ZSWatch/Extension-HW/production/extension-CHECKED/HTML/images/cat_pdf_drill_map_ZSWatch-Extension-NPTH_drill_map.png

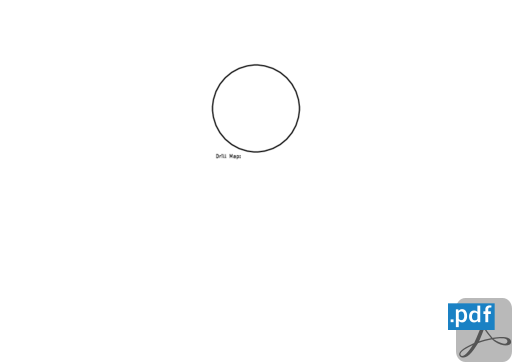
production/extension-CHECKED/HTML/images/cat_pdf_drill_map_ZSWatch-Extension-NPTH_drill_map.png
