ZSWatch/Extension-HW/production/extension-CHECKED/HTML/images/cat_png_3d_viewer_angled_top_ZSWatch-Extension-angled_top.png

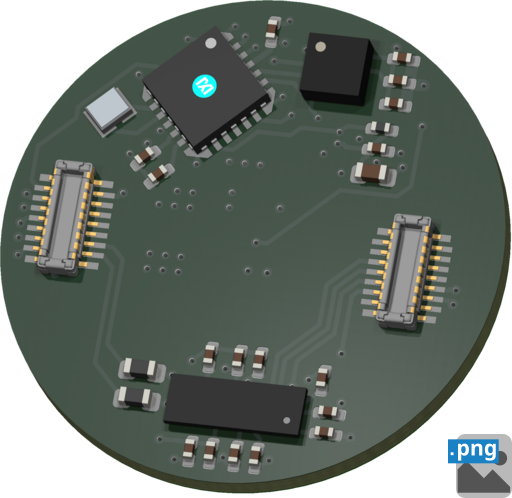
production/extension-CHECKED/HTML/images/cat_png_3d_viewer_angled_top_ZSWatch-Extension-angled_top.png
