ZSWatch/Extension-HW/production/extension-CHECKED/Manufacturing/Fabrication/ZSWatch-Extension-fabrication.pdf

# Top Fabrication (Scale 1:1)

# Heartrate-HW Fabrication Document

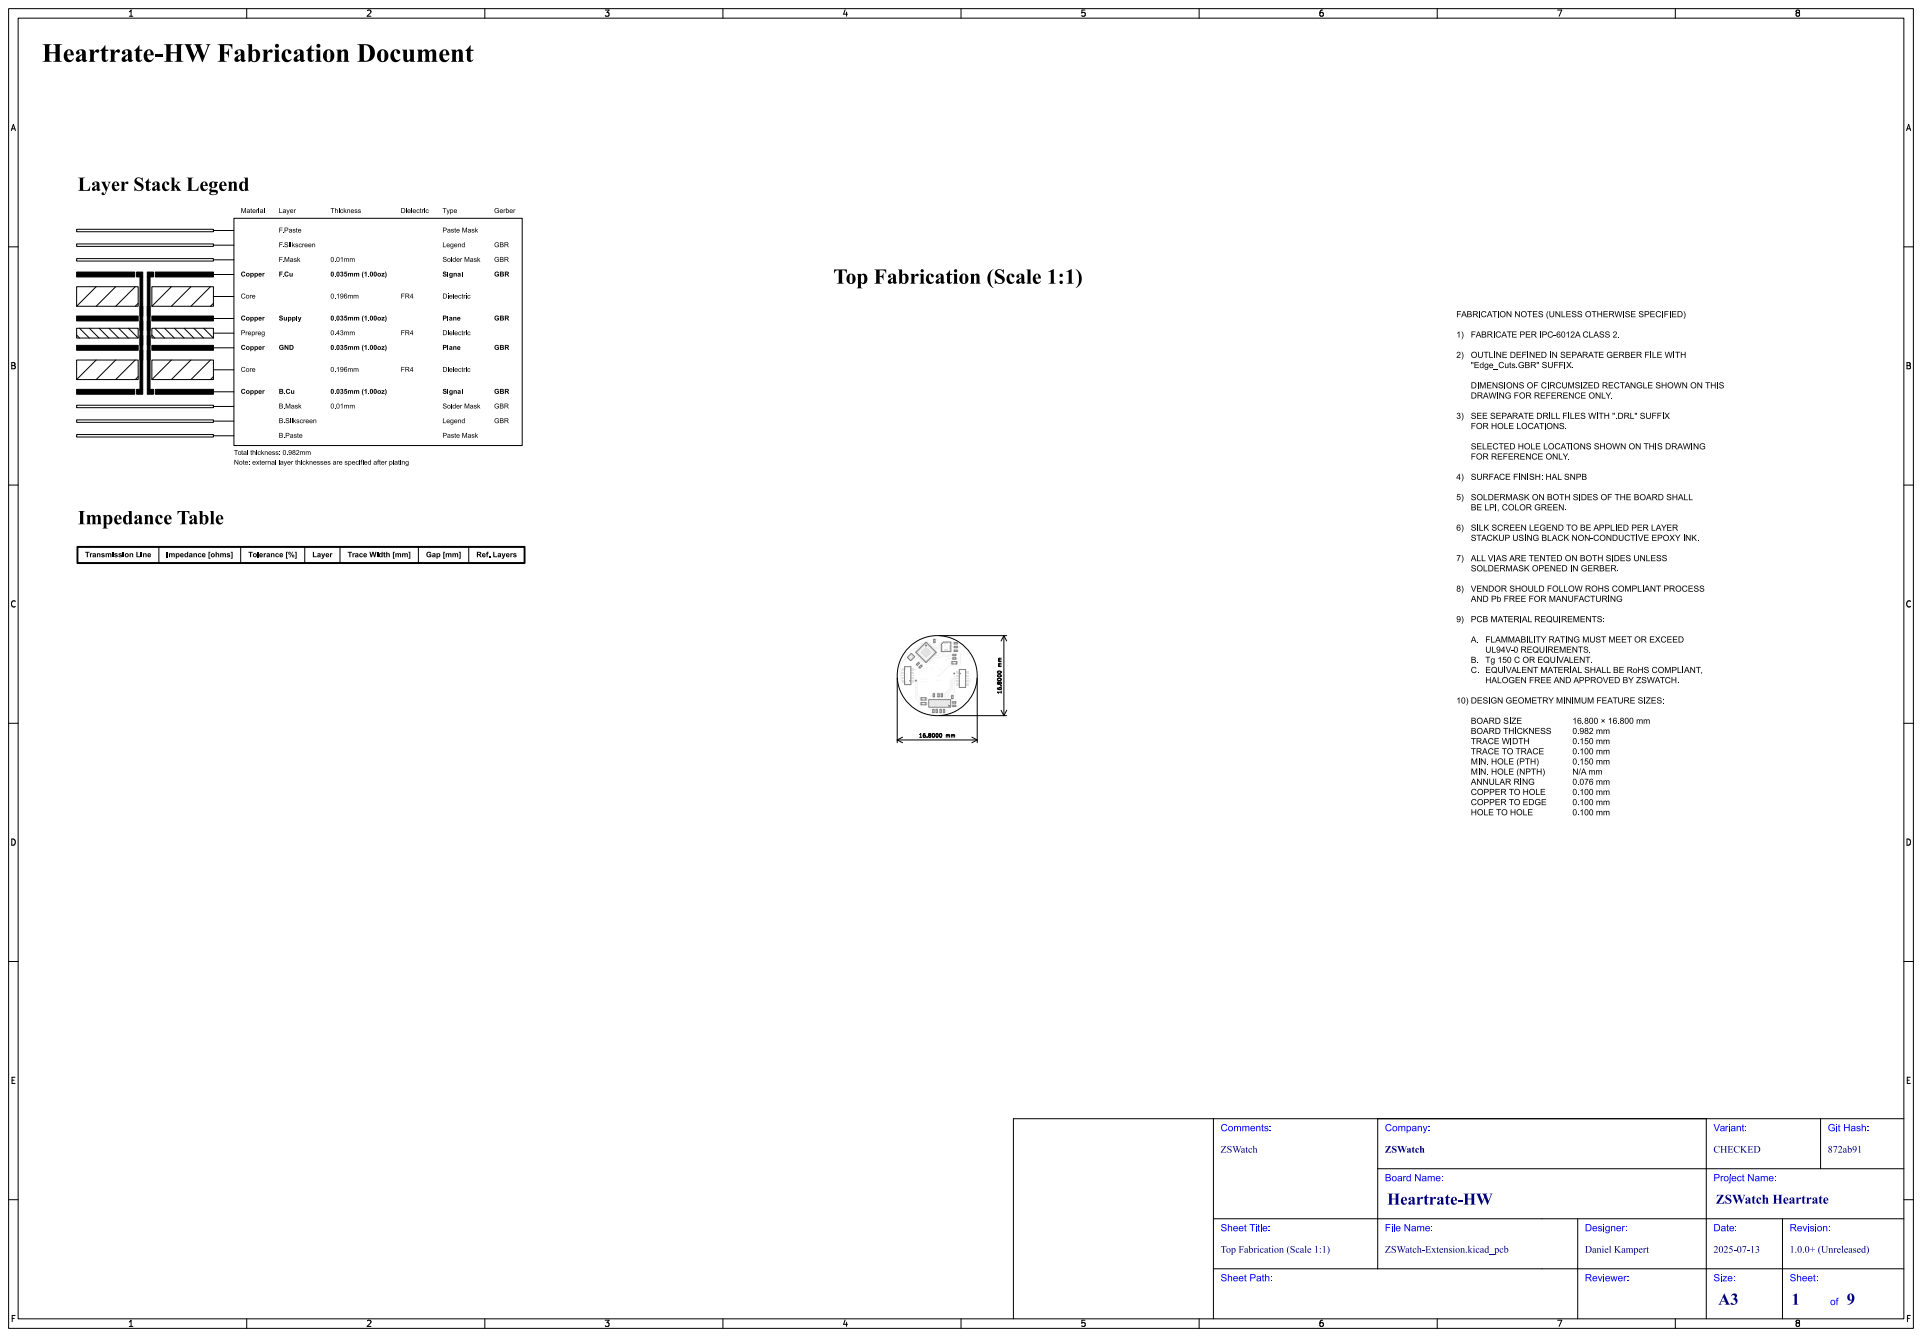
[picture p11: page 1]
Git Hash:; ZSWatch; Comments:; Sheet Path:; Sheet Title:; File Name:; Heartrate-HW; ZSWatch Heartrate; Company:; CHECKED; Variant:; Board Name:; ZSWatch-Extension.kicad_pcb; Daniel Kampert; Designer:; Reviewer:; Project Name:; Date:; 1.0.0+ (Unreleased); Revision:; Size:; Sheet:

Top Fabrication (Scale 1:1)

# Bottom Fabrication (Scale 1:1)

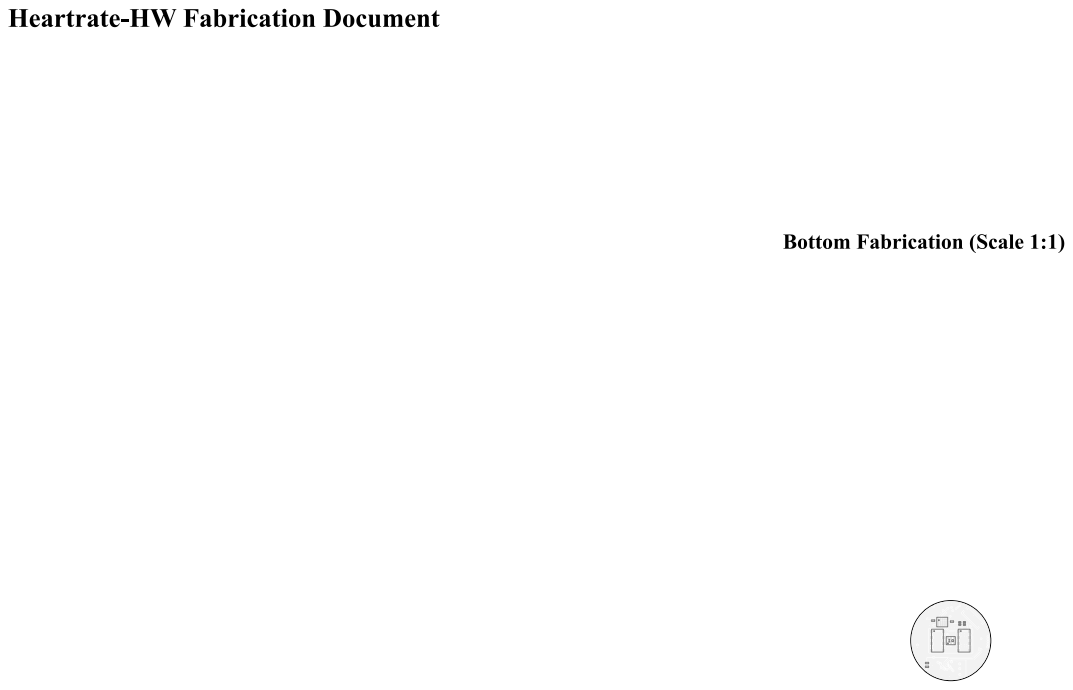
[picture p12: page 2]
Git; Hash:; ZSWatch; Comments:; Sheet Title:; File Name:; Heartrate-HW; ZSWatch Heartrate; Company:; CHECKED; Variant:; Board Name:; ZSWatch-Extension.kicad_pcb; Daniel Kampert; Designer:; Project Name:; Date:; 1.0.0+ (Unreleased); Revision:

Bottom Fabrication (Scale 1:1)

# Drill Drawing L1 - L4 (Scale 1:1)

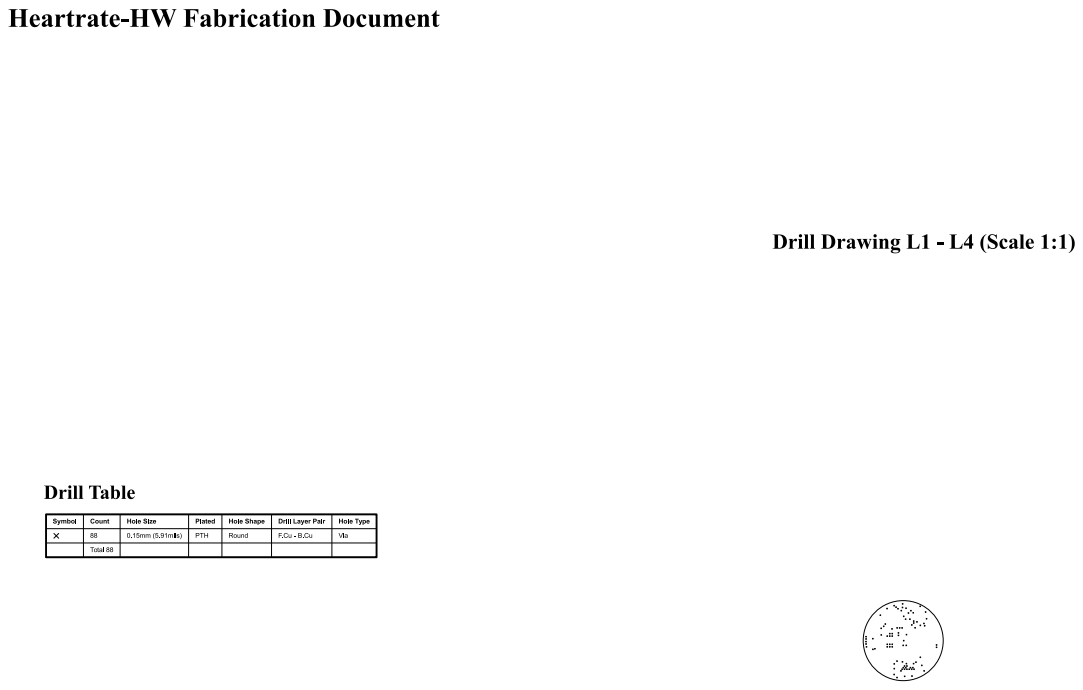
[picture p13: page 3]
Git; Hash:; ZSWatch; Comments:; Drill Drawing (L1 - L4); Sheet Title:; File Name:; Heartrate-HW; ZSWatch Heartrate; Company:; CHECKED; Variant:; Board Name:; ZSWatch-Extension.kicad_pcb; Daniel Kampert; Designer:; Project Name:; Date:; 1.0.0+ (Unreleased); Revision:

# Top Test Points (Scale 1:1)

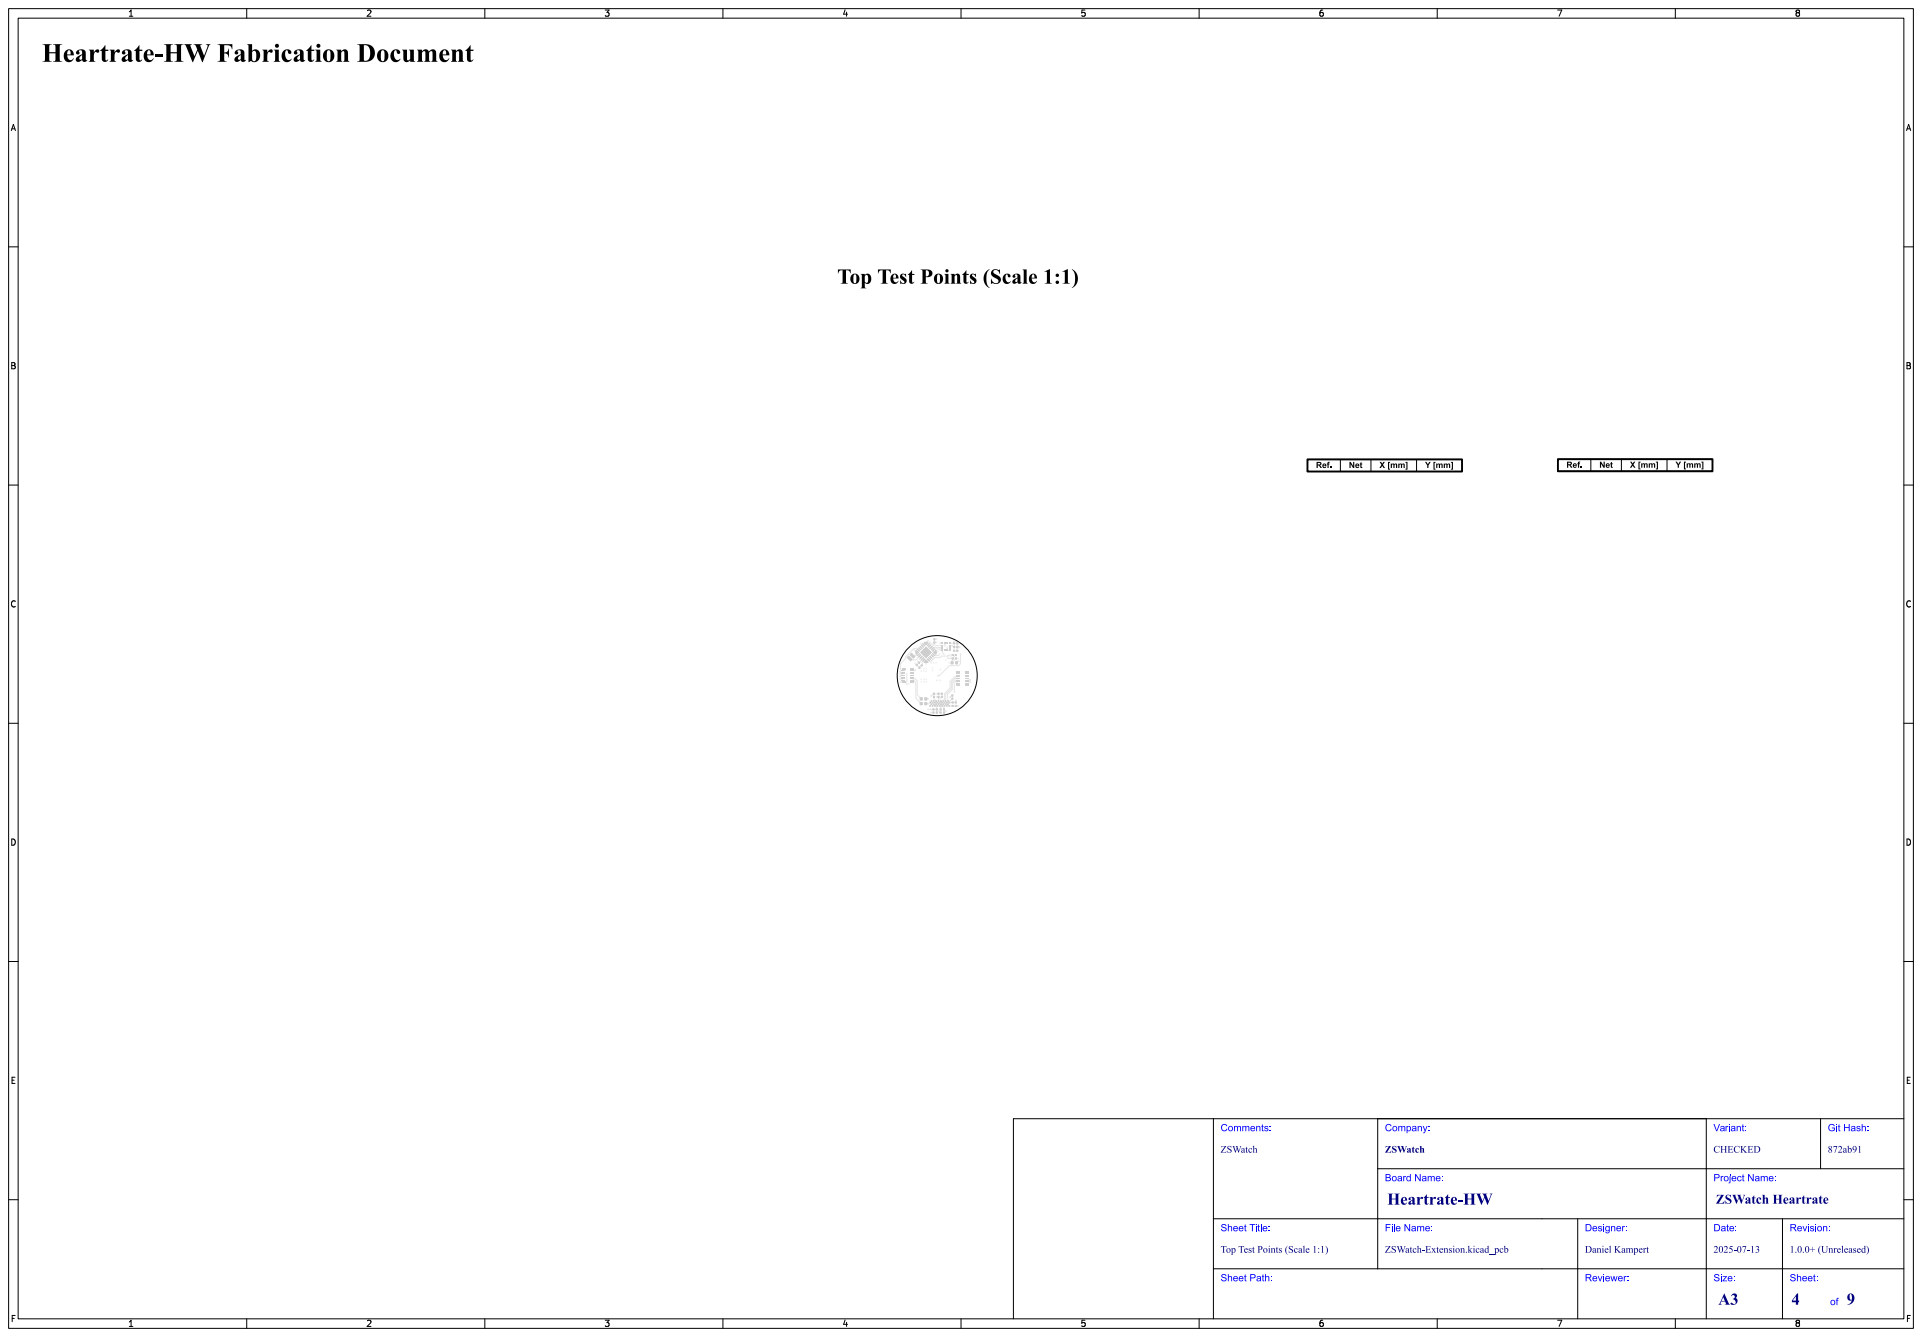
[picture p14: page 4]
Git; Hash:; ZSWatch; Comments:; Sheet Title:; File Name:; Heartrate-HW; ZSWatch Heartrate; Company:; CHECKED; Variant:; Board Name:; ZSWatch-Extension.kicad_pcb; Daniel Kampert; Designer:; Project Name:; Date:; 1.0.0+ (Unreleased); Revision:

Top Test Points (Scale 1:1)

# Bottom Test Points (Scale 1:1)

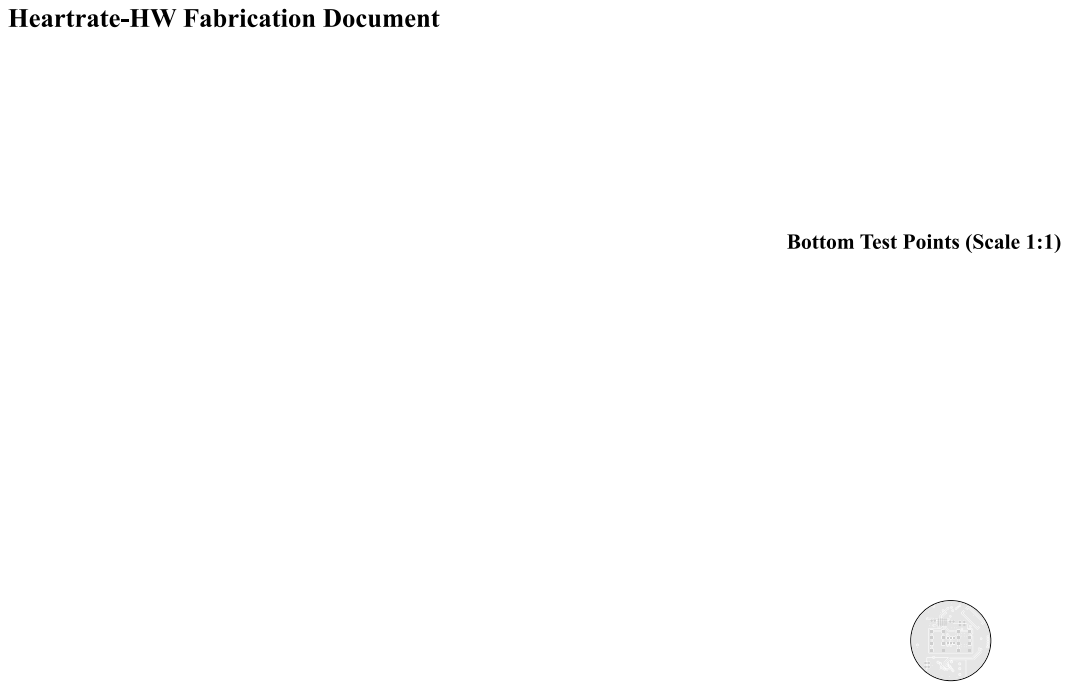
[picture p15: page 5]
Git; Hash:; ZSWatch; Comments:; Sheet Title:; File Name:; Heartrate-HW; ZSWatch Heartrate; Company:; CHECKED; Variant:; Board Name:; ZSWatch-Extension.kicad_pcb; Daniel Kampert; Designer:; Project Name:; Date:; 1.0.0+ (Unreleased); Revision:

Bottom Test Points (Scale 1:1)

# F.Cu (Scale 1:1)

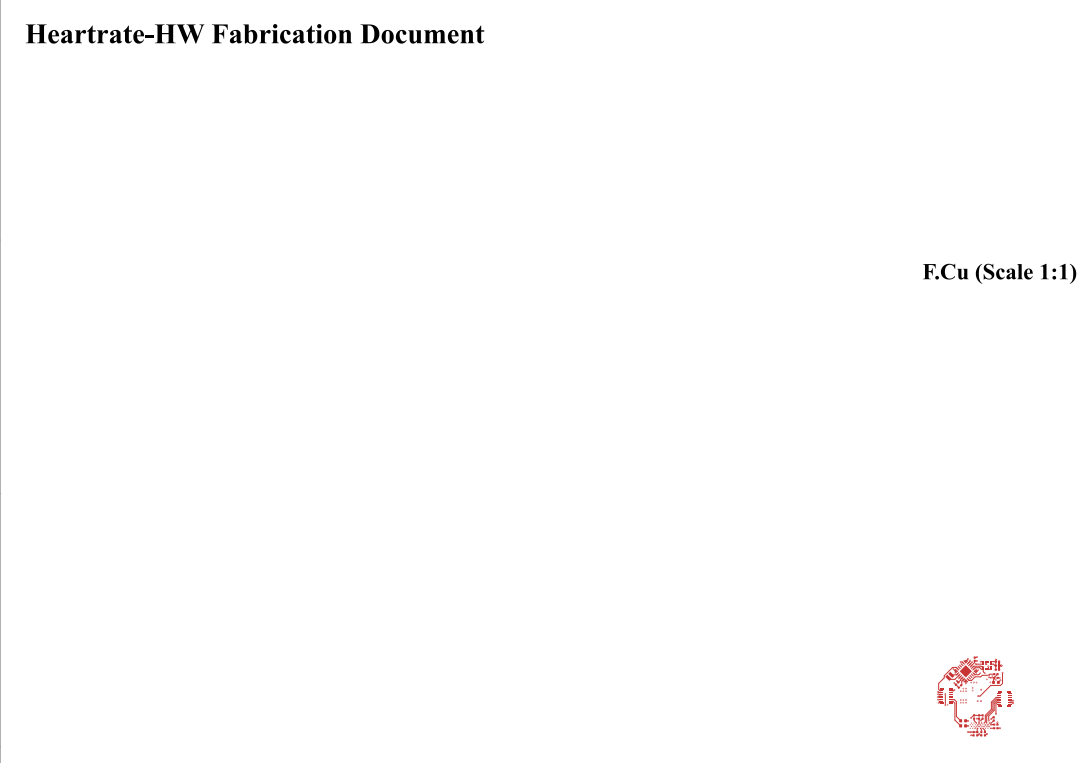
[picture p16: page 6]
Git; Hash:; ZSWatch; Comments:; F.Cu (Scale 1:1); Sheet Title:; File Name:; Heartrate-HW; ZSWatch Heartrate; Company:; CHECKED; Variant:; Board Name:; ZSWatch-Extension.kicad_pcb; Daniel Kampert; Designer:; Project Name:; Date:; 1.0.0+ (Unreleased); Revision:

# Supply (Scale 1:1)

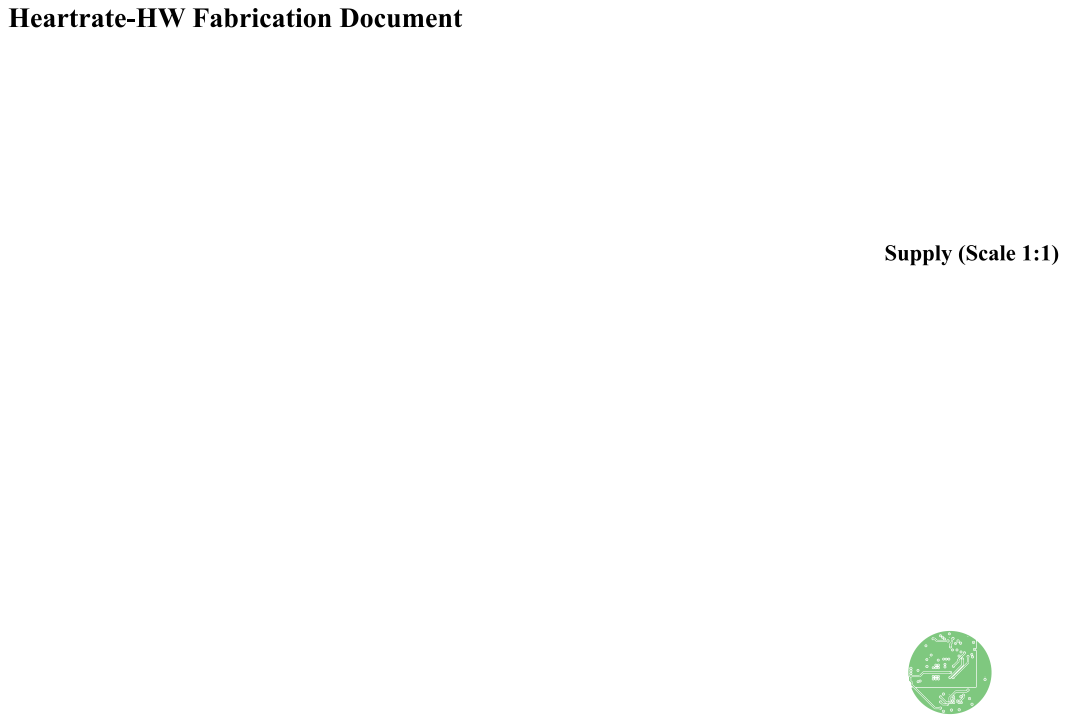
[picture p17: page 7]
Git; Hash:; ZSWatch; Comments:; Supply (Scale 1:1); Sheet Title:; File Name:; Heartrate-HW; ZSWatch Heartrate; Company:; CHECKED; Variant:; Board Name:; ZSWatch-Extension.kicad_pcb; Daniel Kampert; Designer:; Project Name:; Date:; 1.0.0+ (Unreleased); Revision:

# GND (Scale 1:1)

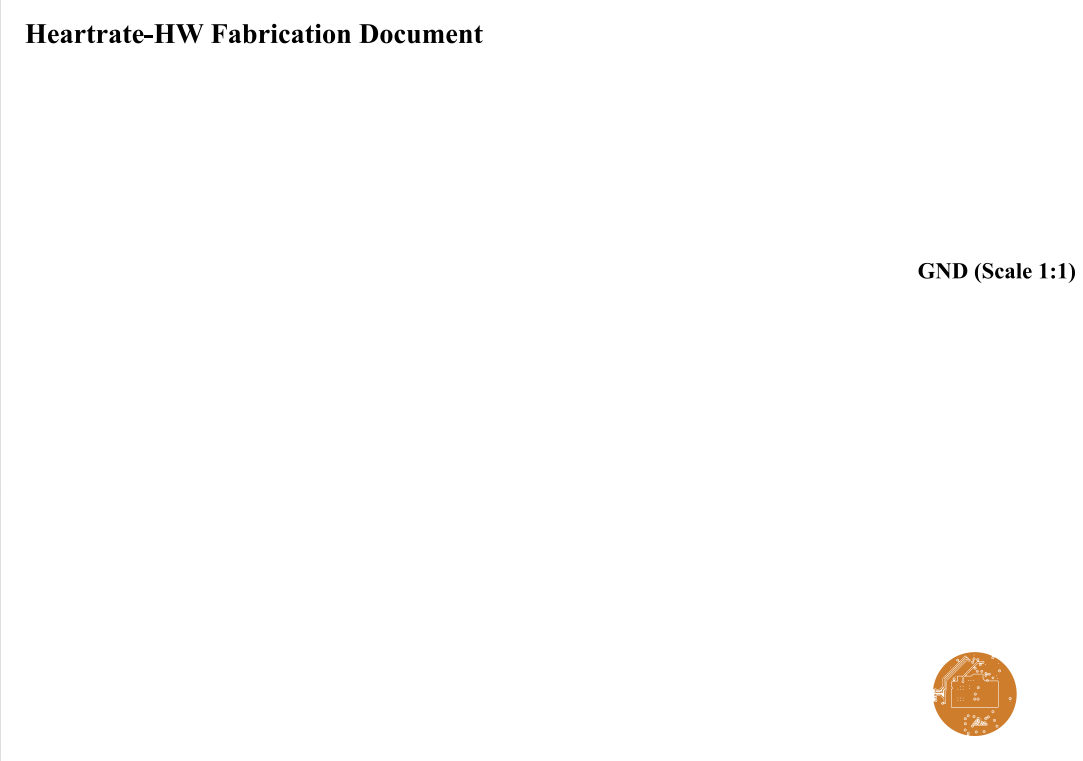
[picture p18: page 8]
Git; Hash:; ZSWatch; Comments:; GND (Scale 1:1); Sheet Title:; File Name:; Heartrate-HW; ZSWatch Heartrate; Company:; CHECKED; Variant:; Board Name:; ZSWatch-Extension.kicad_pcb; Daniel Kampert; Designer:; Project Name:; Date:; 1.0.0+ (Unreleased); Revision:

# B.Cu (Scale 1:1)

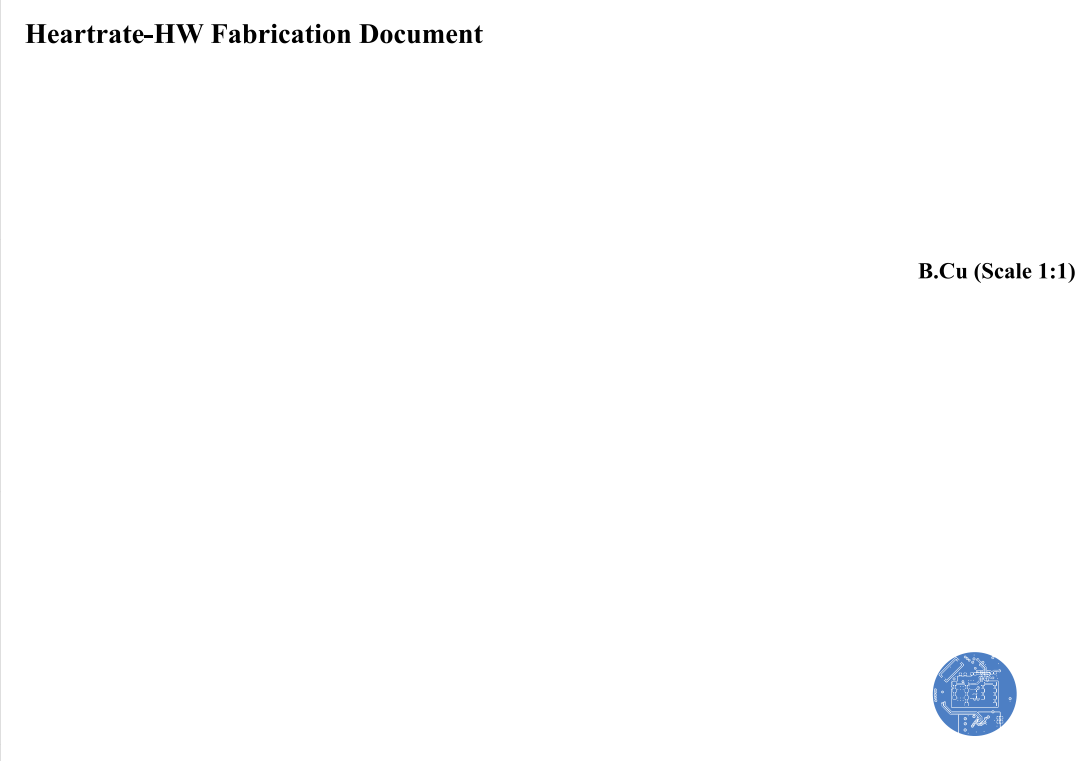
[picture p19: page 9]
Git; Hash:; ZSWatch; Comments:; B.Cu (Scale 1:1); Sheet Title:; File Name:; Heartrate-HW; ZSWatch Heartrate; Company:; CHECKED; Variant:; Board Name:; ZSWatch-Extension.kicad_pcb; Daniel Kampert; Designer:; Project Name:; Date:; 1.0.0+ (Unreleased); Revision:
