ZSWatch/Extension-HW/production/extension-PRELIMINARY/Manufacturing/Fabrication/ZSWatch-Extension-fabrication.pdf

# Top Fabrication (Scale 1:1)

# Heartrate-HW Fabrication Document

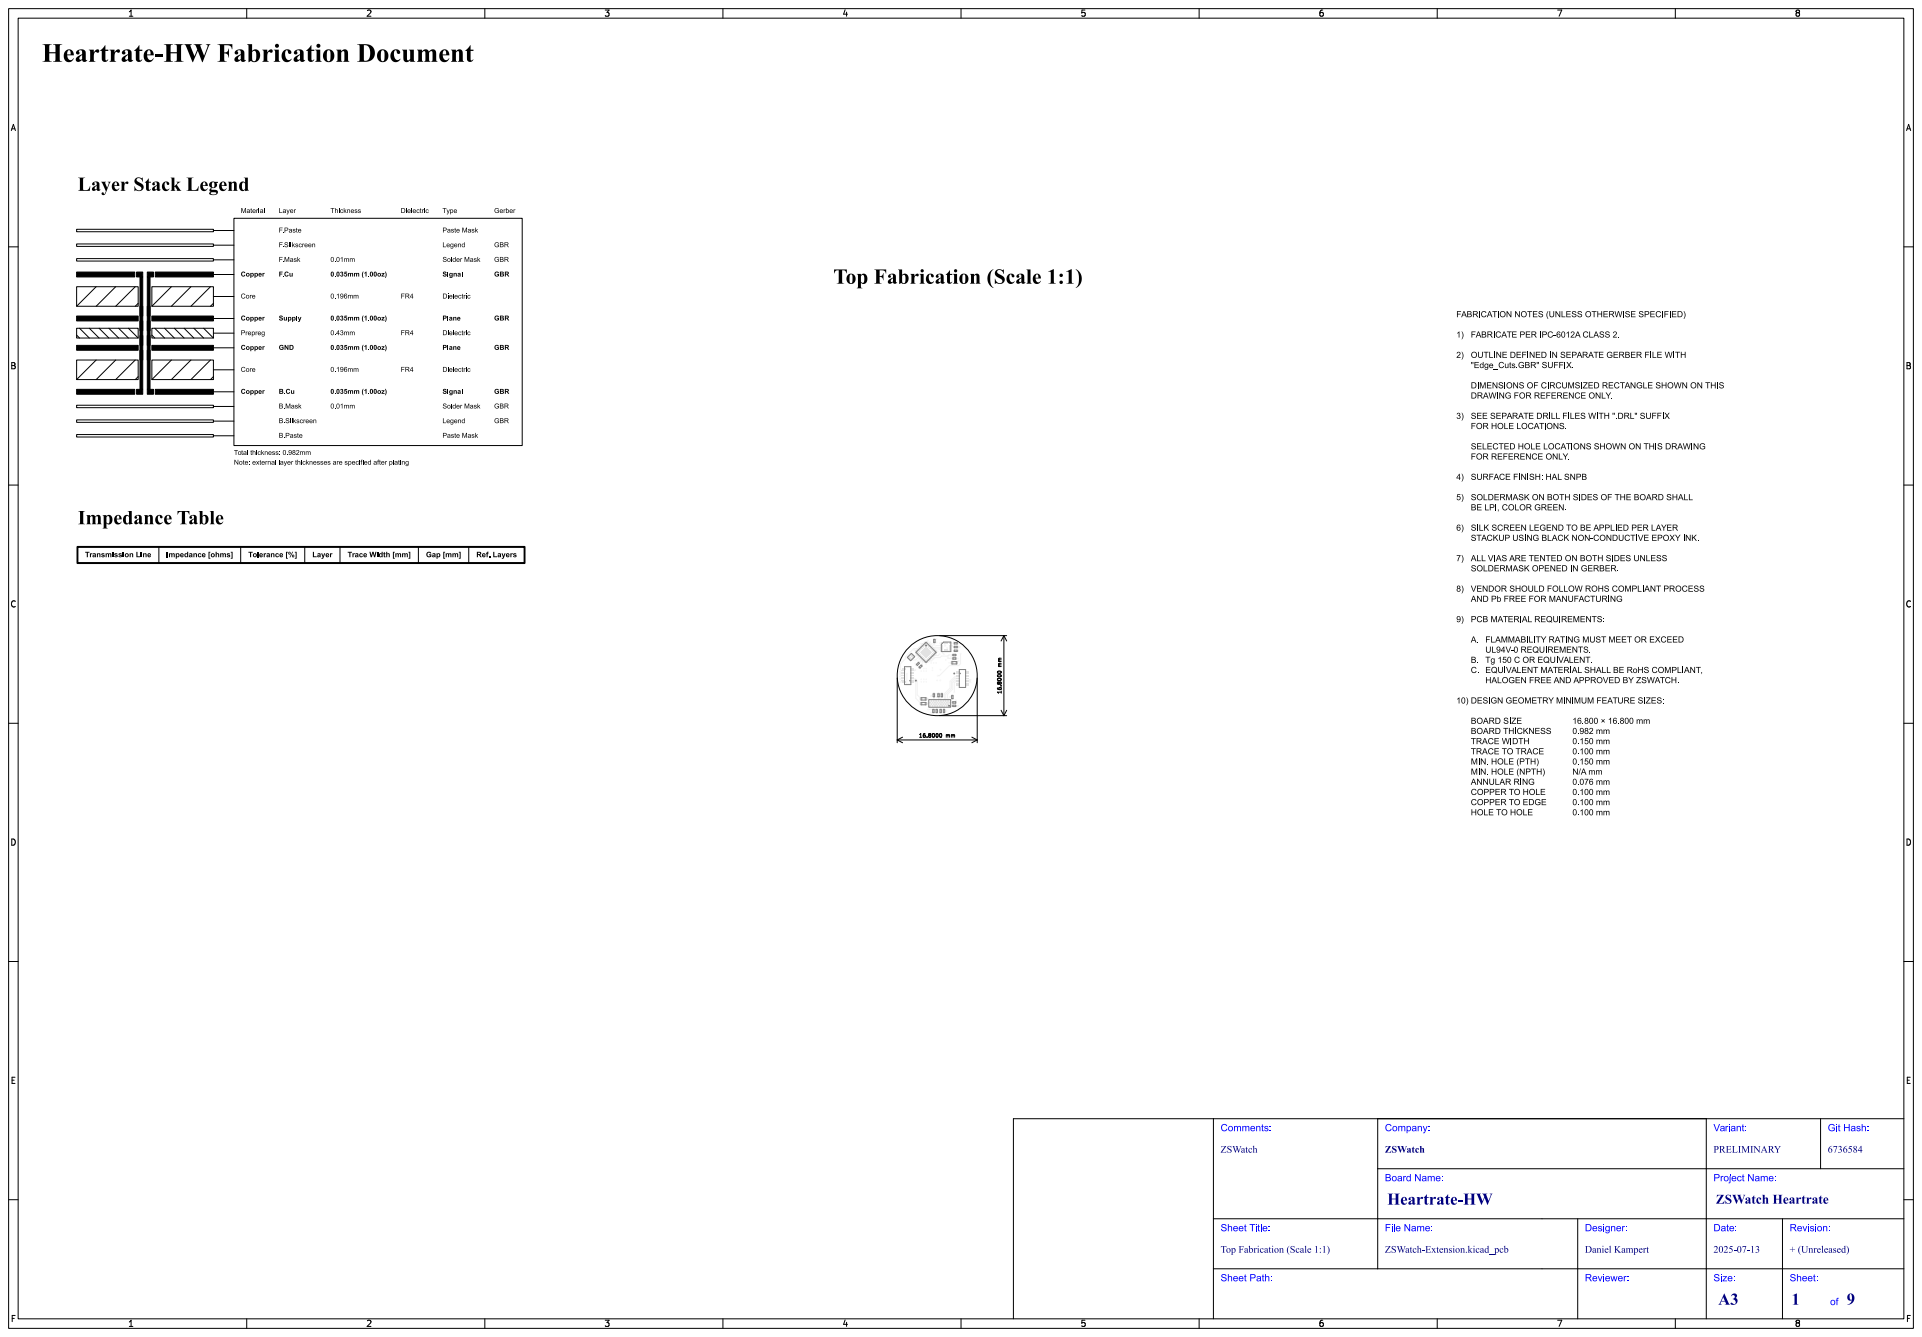
[picture p20: page 1]
Git Hash:; ZSWatch; Comments:; Sheet Path:; Sheet Title:; File Name:; Heartrate-HW; ZSWatch Heartrate; Company:; PRELIMINARY; Variant:; Board Name:; ZSWatch-Extension.kicad_pcb; Daniel Kampert; Designer:; Reviewer:; Project Name:; Date:; + (Unreleased); Revision:; Size:; Sheet:

Top Fabrication (Scale 1:1)

# Bottom Fabrication (Scale 1:1)

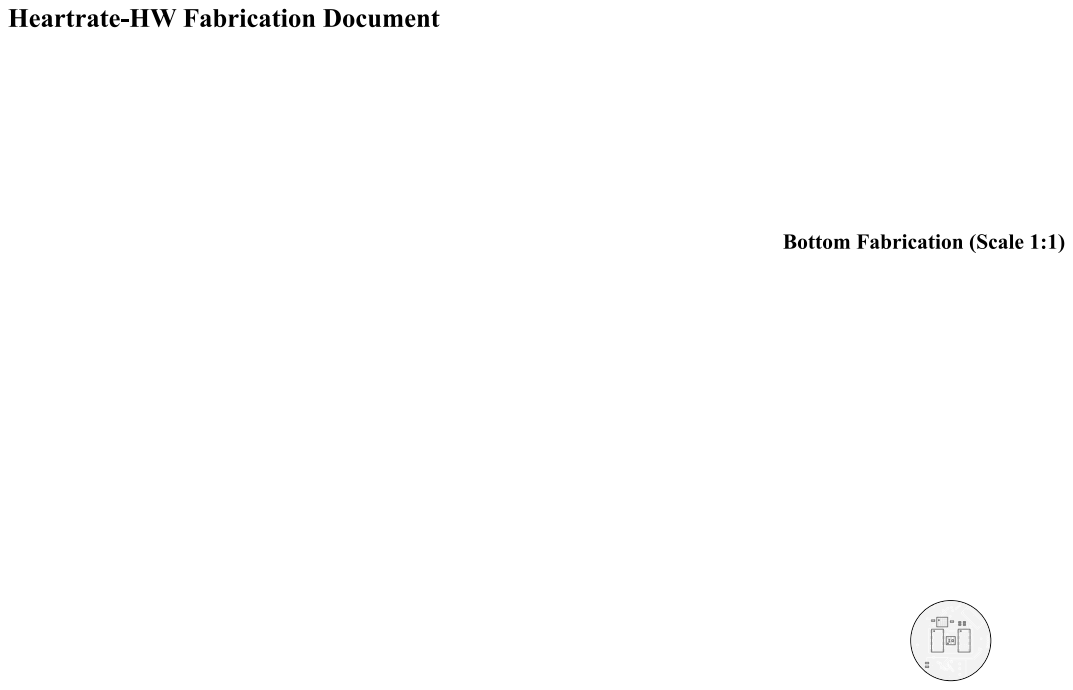
[picture p21: page 2]
Git; Hash:; ZSWatch; Comments:; Sheet Title:; File Name:; Heartrate-HW; ZSWatch Heartrate; Company:; PRELIMINARY; Variant:; Board Name:; ZSWatch-Extension.kicad_pcb; Daniel Kampert; Designer:; Project Name:; Date:; + (Unreleased); Revision:

Bottom Fabrication (Scale 1:1)

# Drill Drawing L1 - L4 (Scale 1:1)

Git; Hash:; ZSWatch; Comments:; Drill Drawing (L1 - L4); Sheet Title:; File Name:; Heartrate-HW; ZSWatch Heartrate; Company:; PRELIMINARY; Variant:; Board Name:; ZSWatch-Extension.kicad_pcb; Daniel Kampert; Designer:; Project Name:; Date:; + (Unreleased); Revision:

# Top Test Points (Scale 1:1)

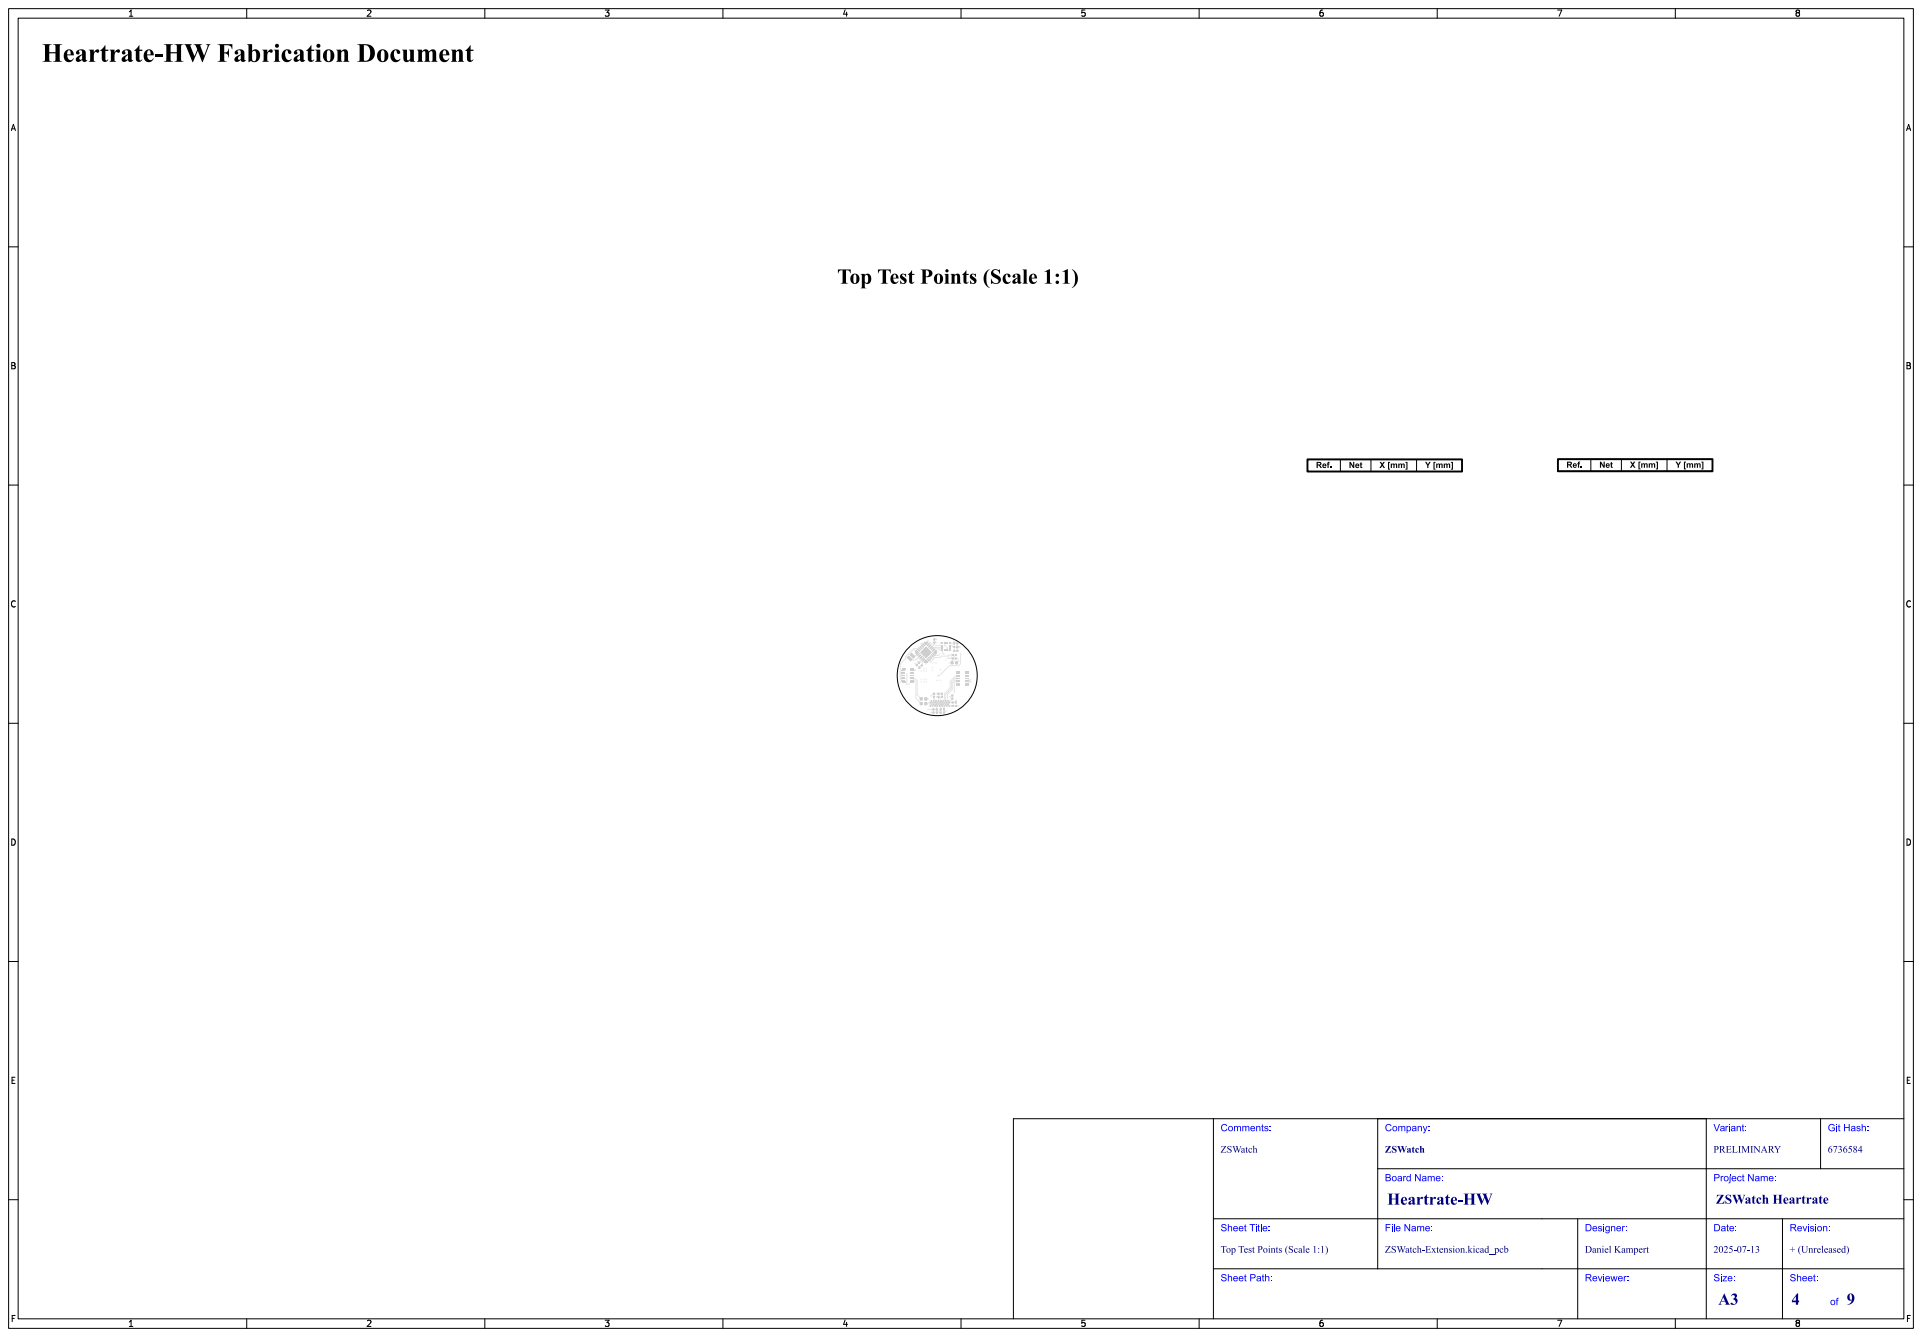
[picture p22: page 4]
Git; Hash:; ZSWatch; Comments:; Sheet Title:; File Name:; Heartrate-HW; ZSWatch Heartrate; Company:; PRELIMINARY; Variant:; Board Name:; ZSWatch-Extension.kicad_pcb; Daniel Kampert; Designer:; Project Name:; Date:; + (Unreleased); Revision:

Top Test Points (Scale 1:1)

# Bottom Test Points (Scale 1:1)

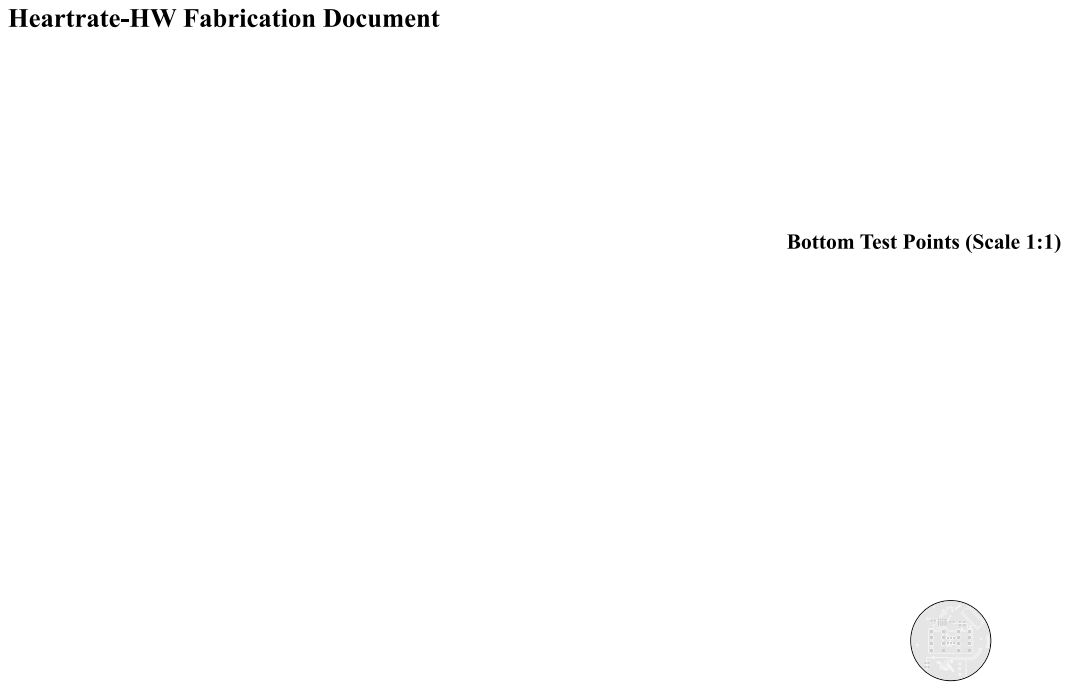
[picture p23: page 5]
Git; Hash:; ZSWatch; Comments:; Sheet Title:; File Name:; Heartrate-HW; ZSWatch Heartrate; Company:; PRELIMINARY; Variant:; Board Name:; ZSWatch-Extension.kicad_pcb; Daniel Kampert; Designer:; Project Name:; Date:; + (Unreleased); Revision:

Bottom Test Points (Scale 1:1)

# F.Cu (Scale 1:1)

Git; Hash:; ZSWatch; Comments:; F.Cu (Scale 1:1); Sheet Title:; File Name:; Heartrate-HW; ZSWatch Heartrate; Company:; PRELIMINARY; Variant:; Board Name:; ZSWatch-Extension.kicad_pcb; Daniel Kampert; Designer:; Project Name:; Date:; + (Unreleased); Revision:

# Supply (Scale 1:1)

Git; Hash:; ZSWatch; Comments:; Supply (Scale 1:1); Sheet Title:; File Name:; Heartrate-HW; ZSWatch Heartrate; Company:; PRELIMINARY; Variant:; Board Name:; ZSWatch-Extension.kicad_pcb; Daniel Kampert; Designer:; Project Name:; Date:; + (Unreleased); Revision:

# GND (Scale 1:1)

Git; Hash:; ZSWatch; Comments:; GND (Scale 1:1); Sheet Title:; File Name:; Heartrate-HW; ZSWatch Heartrate; Company:; PRELIMINARY; Variant:; Board Name:; ZSWatch-Extension.kicad_pcb; Daniel Kampert; Designer:; Project Name:; Date:; + (Unreleased); Revision:

# B.Cu (Scale 1:1)

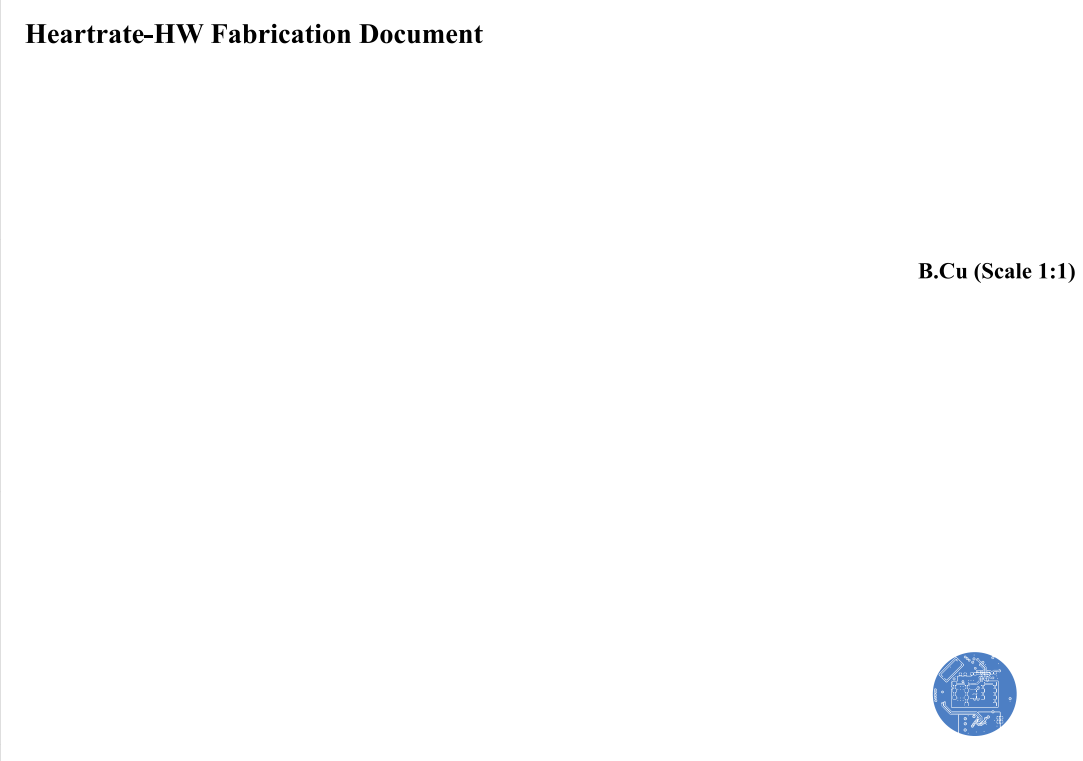
[picture p24: page 9]
Git; Hash:; ZSWatch; Comments:; B.Cu (Scale 1:1); Sheet Title:; File Name:; Heartrate-HW; ZSWatch Heartrate; Company:; PRELIMINARY; Variant:; Board Name:; ZSWatch-Extension.kicad_pcb; Daniel Kampert; Designer:; Project Name:; Date:; + (Unreleased); Revision:
