ZSWatch/Extension-HW/production/extension-CHECKED/Manufacturing/Fabrication/Drill Tables/ZSWatch-Extension-(L1-L4)_drill_table.csv

Count | Hole Size | Plated | Hole Shape | Drill Layer Pair | Hole Type
88 | 0.15mm (5.91mils) | PTH | Round | F.Cu - B.Cu | Via
Total 88
