ZSWatch/Extension-HW/production/extension-CHECKED/Manufacturing/Assembly/ZSWatch-Extension-assembly.pdf

# Heartrate-HW Assembly Document

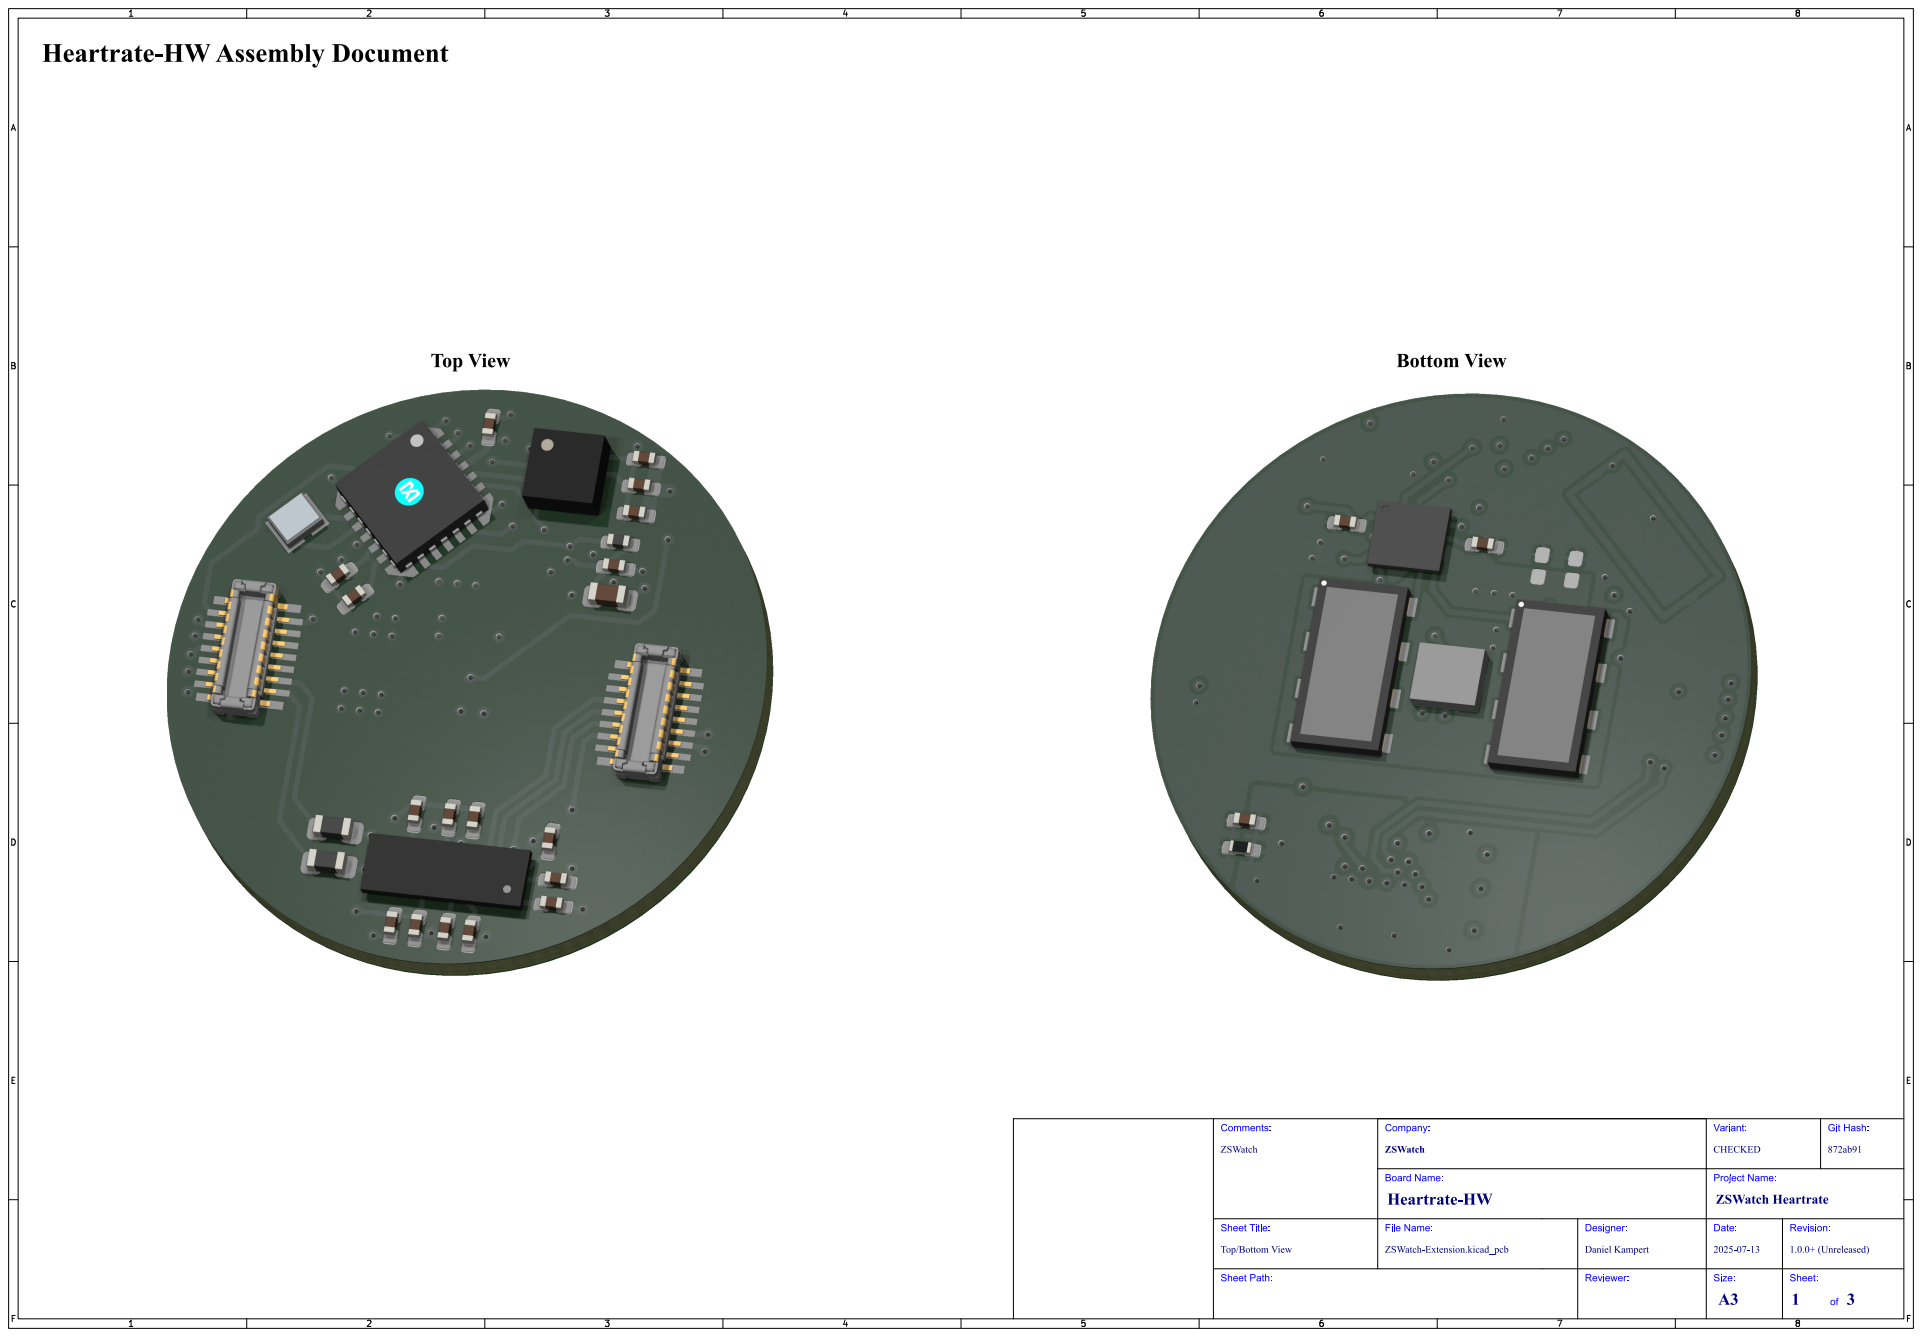
[picture p35: page 1]
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

Top/Bottom View

# Top Assembly (Scale 1:1)


# Bottom Assembly (Scale 1:1)
