ZSWatch/Extension-HW/production/extension-CHECKED/Manufacturing/Fabrication/ZSWatch-Extension-fabrication-5.pdf

# Bottom Test Points (Scale 1:1)

# Heartrate-HW Fabrication Document

Git; Hash:; ZSWatch; Comments:; Sheet Path:; Sheet Title:; File Name:; Heartrate-HW; ZSWatch Heartrate; Company:; CHECKED; Variant:; Board Name:; ZSWatch-Extension.kicad_pcb; Daniel Kampert; Designer:; Reviewer:; Project Name:; Date:; 1.0.0+ (Unreleased); Revision:; Size:; Sheet: 5

Bottom Test Points (Scale 1:1)
