ZSWatch/Extension-HW/production/extension-PRELIMINARY/Manufacturing/Assembly/ZSWatch-Extension-assembly.pdf

# Heartrate-HW Assembly Document

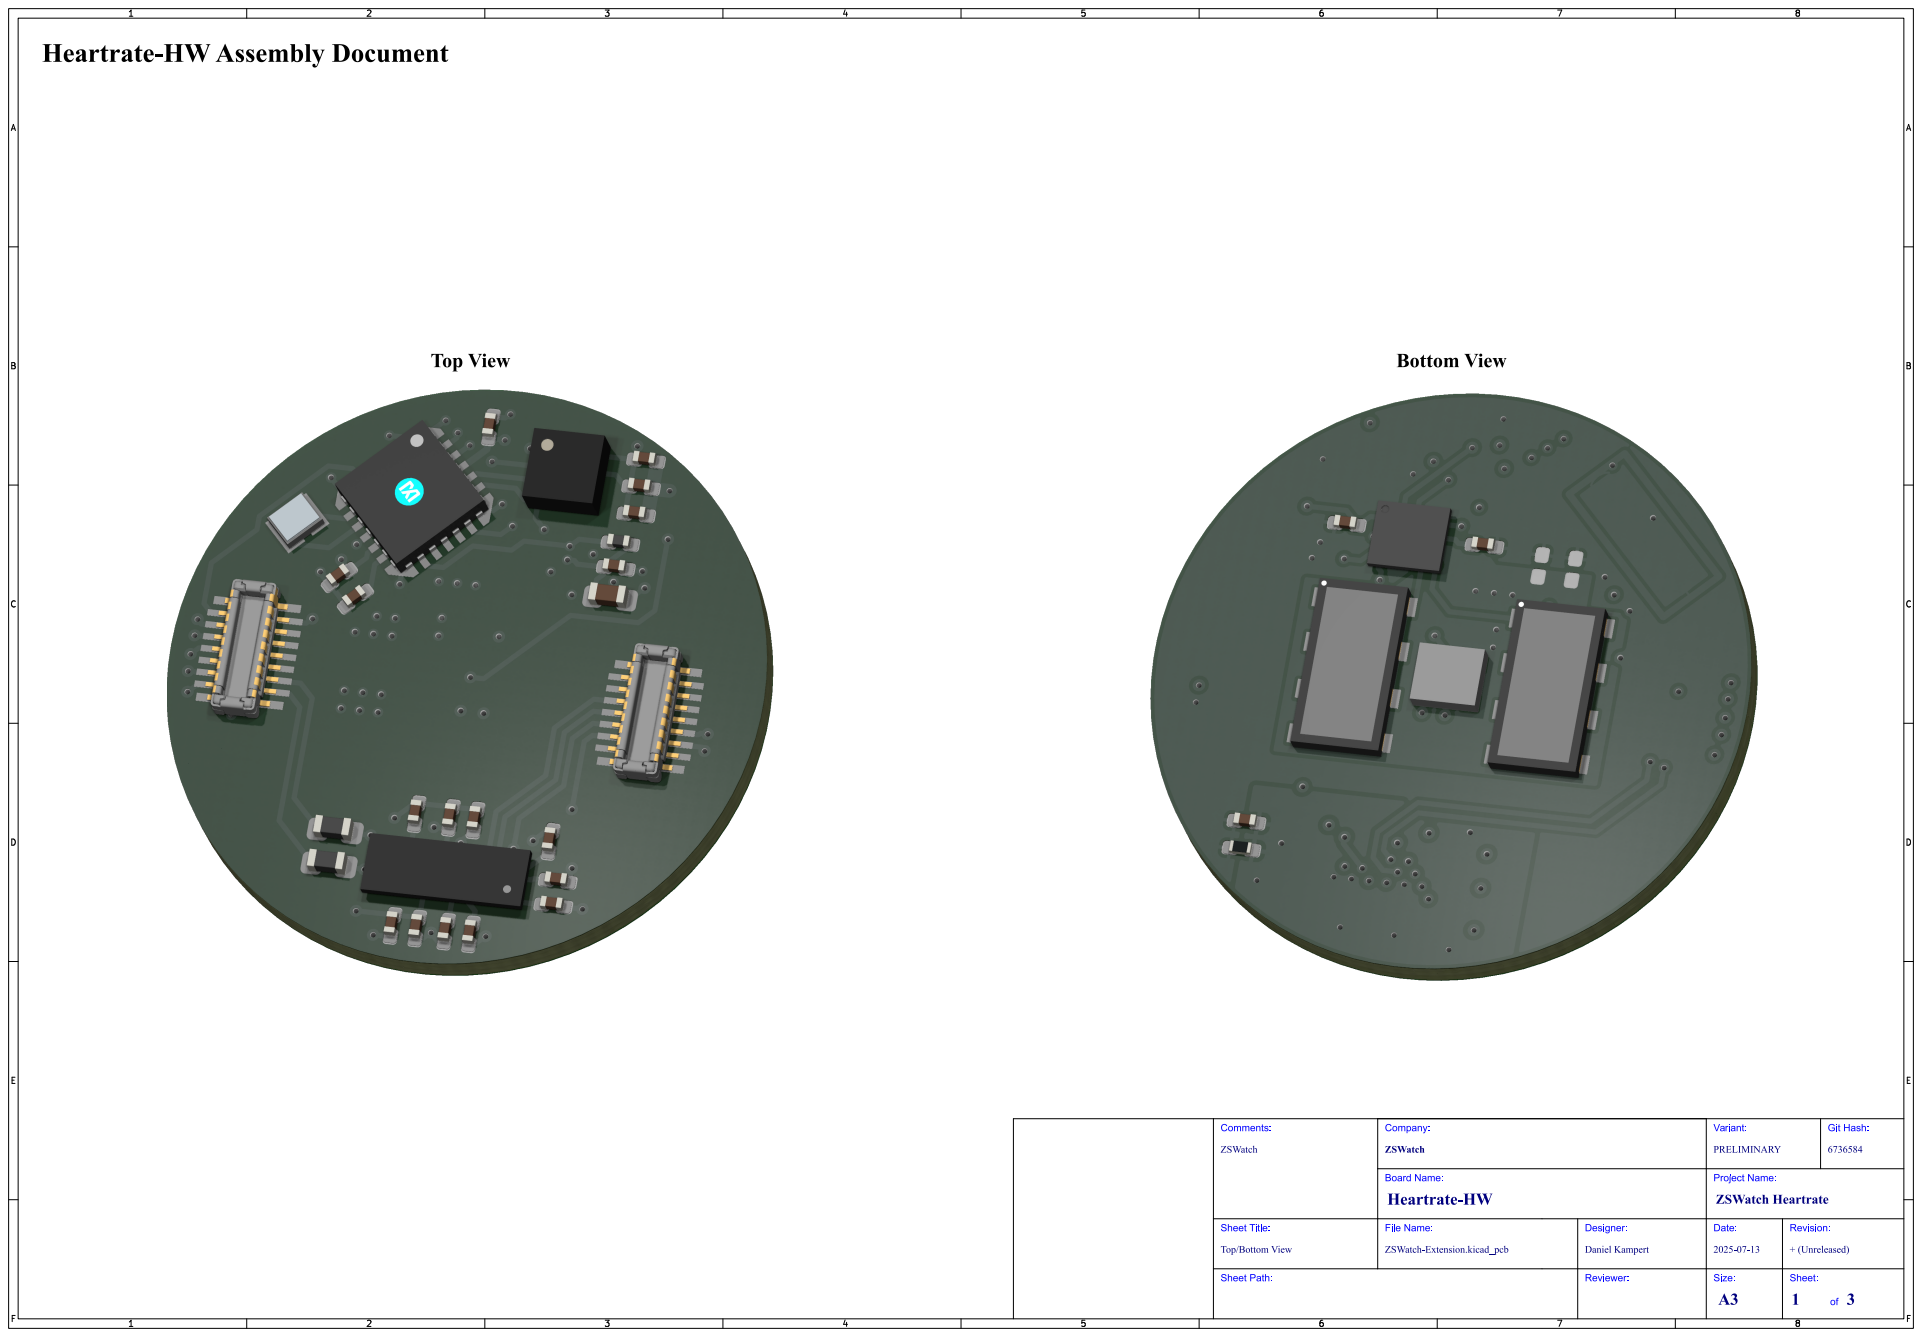
[picture p36: page 1]
Git; Hash:; ZSWatch; Comments:; Sheet Path:; Sheet Title:; File Name:; Heartrate-HW; ZSWatch Heartrate; Company:; PRELIMINARY; Variant:; Board Name:; ZSWatch-Extension.kicad_pcb; Daniel Kampert; Designer:; Reviewer:; Project Name:; Date:; + (Unreleased); Revision:; Size:; Sheet:

Top/Bottom View

# Top Assembly (Scale 1:1)

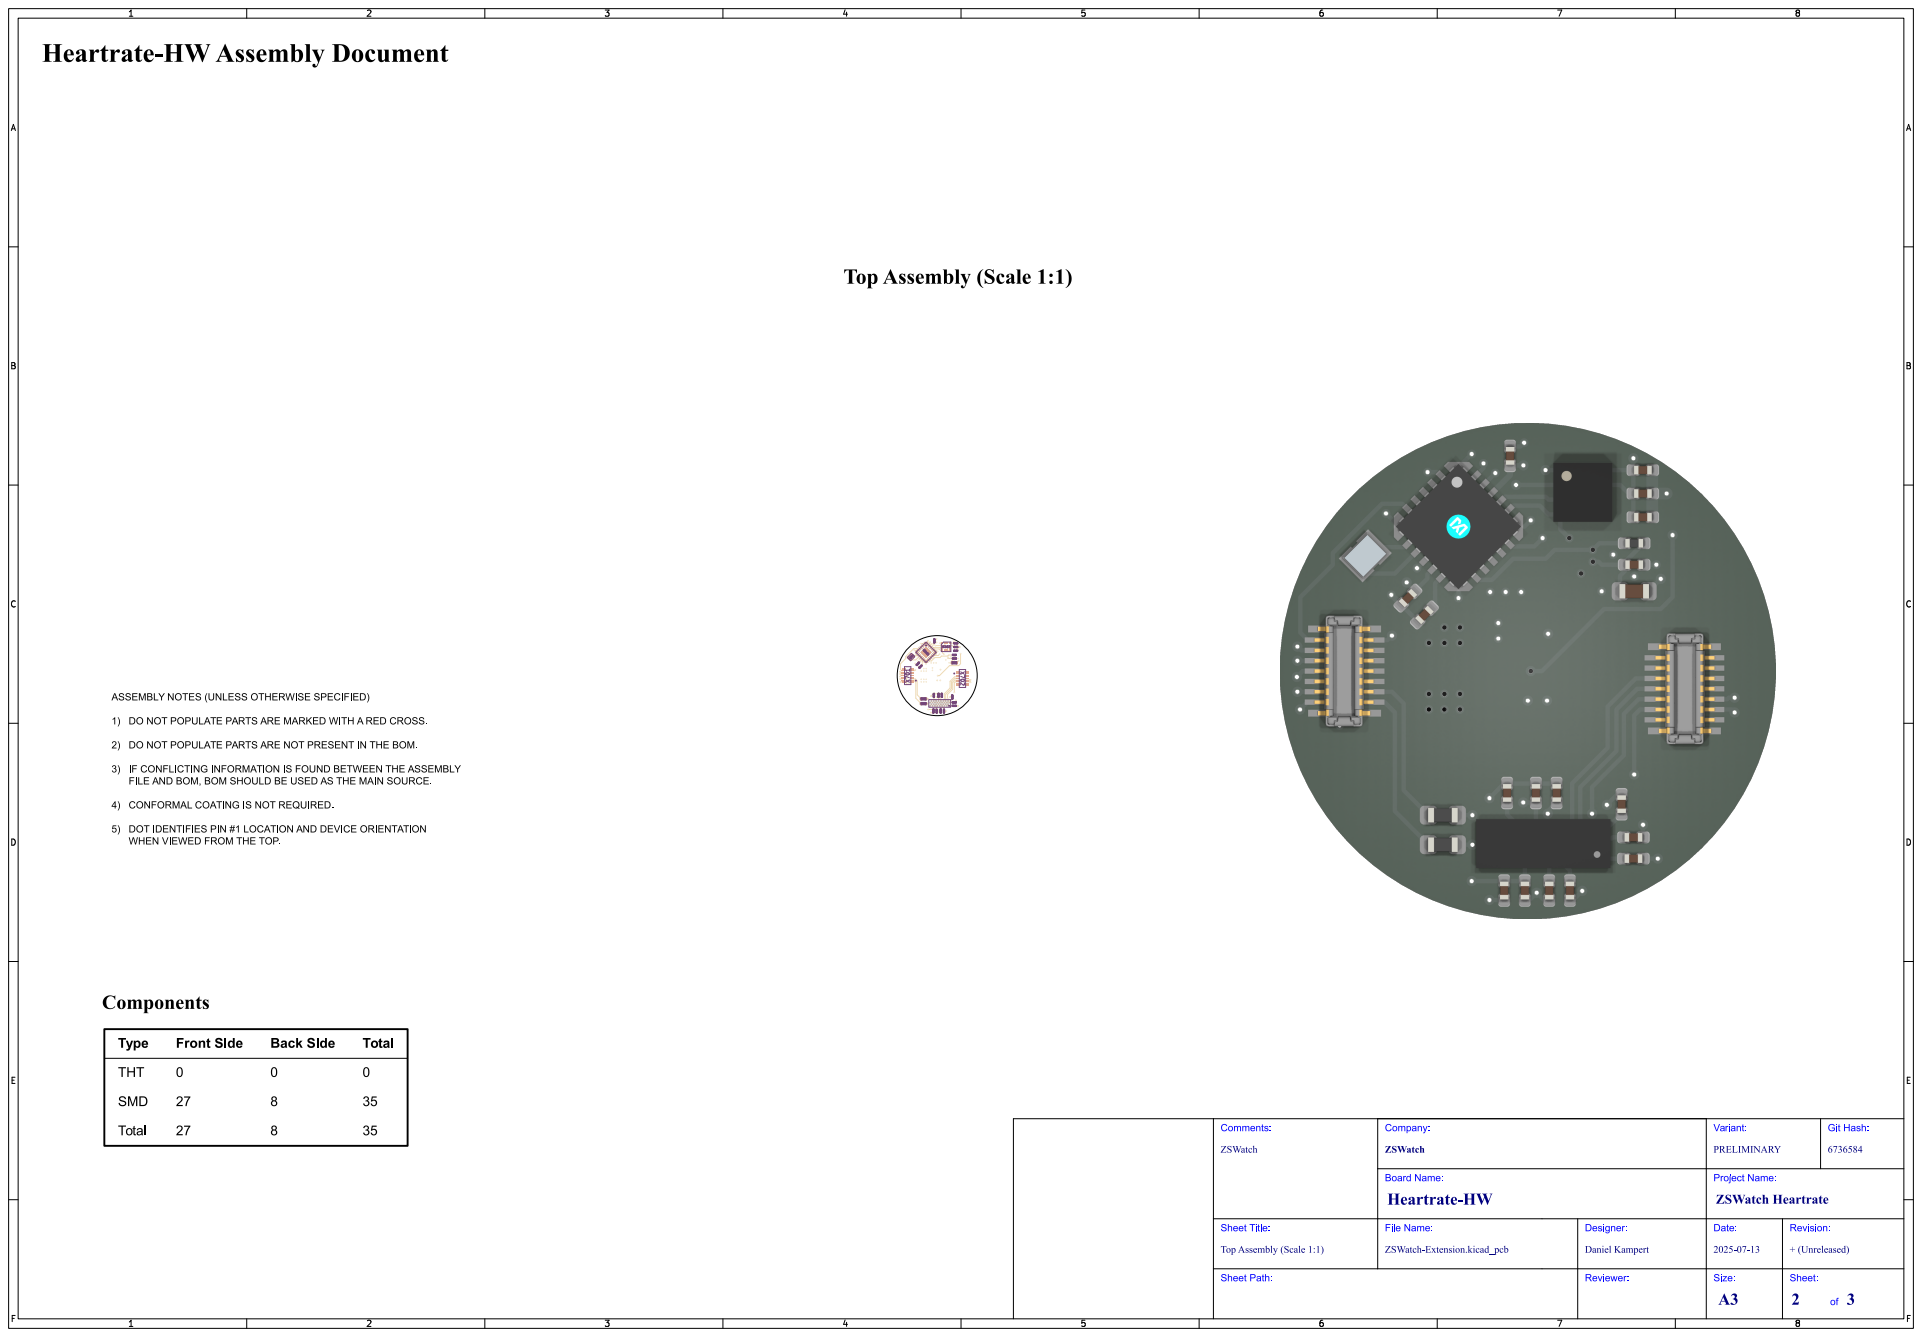
[picture p37: page 2]

# Bottom Assembly (Scale 1:1)

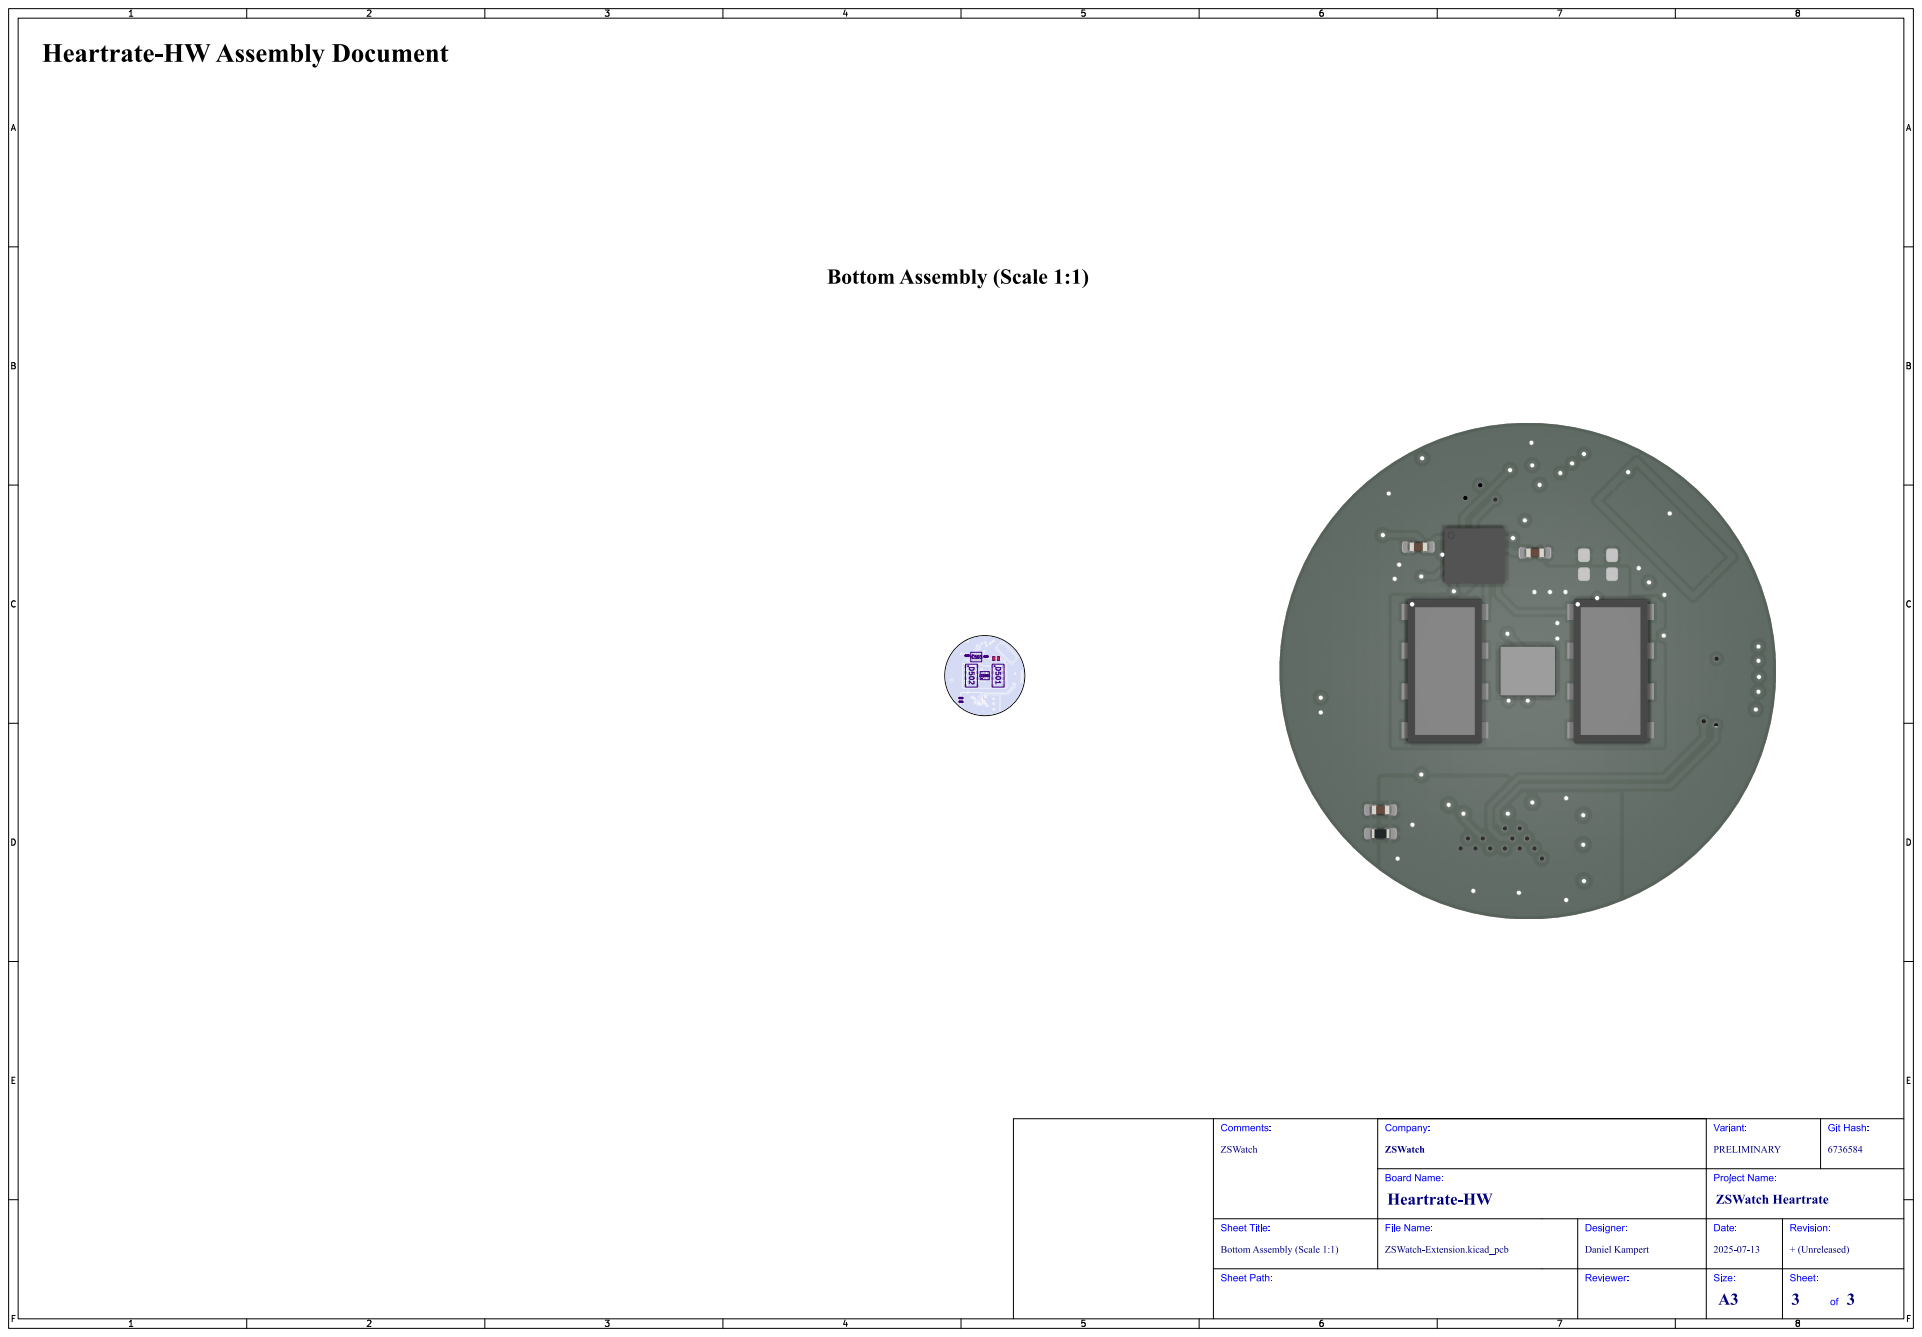
[picture p38: page 3]
