ZSWatch/Extension-HW/production/extension-CHECKED/Manufacturing/Fabrication/Gerbers/ZSWatch-Extension-NPTH_drill_map.pdf

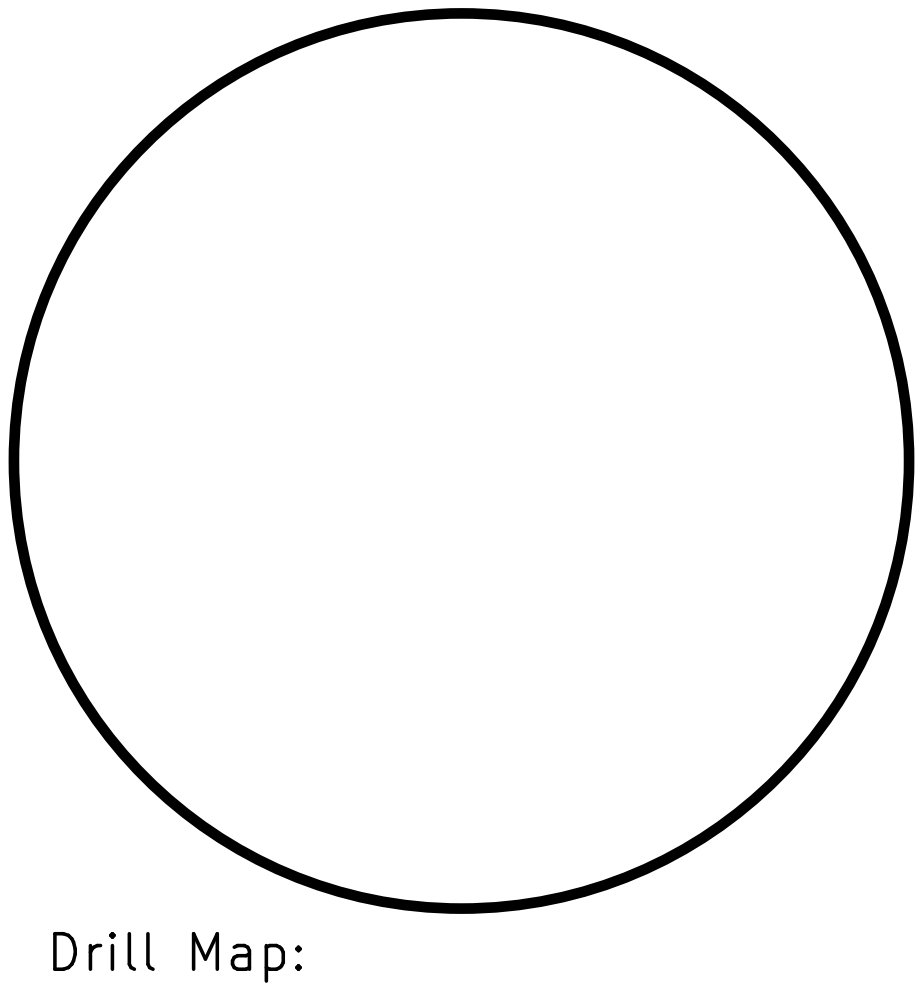
[picture p40: page 1]
