ZSWatch/Extension-HW/production/extension-CHECKED/Manufacturing/Fabrication/Gerbers/ZSWatch-Extension-PTH_drill_map.pdf

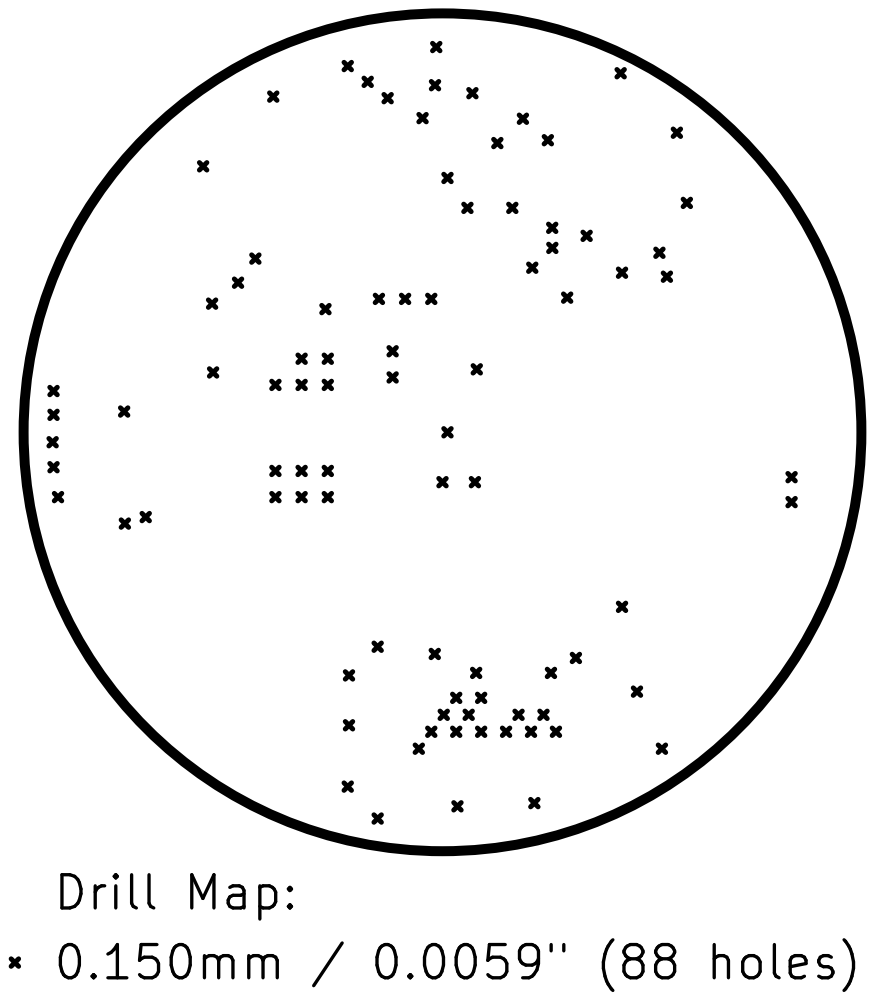
[picture p41: page 1]
